jimd80/party-games-26p/images/microbit-battery.png

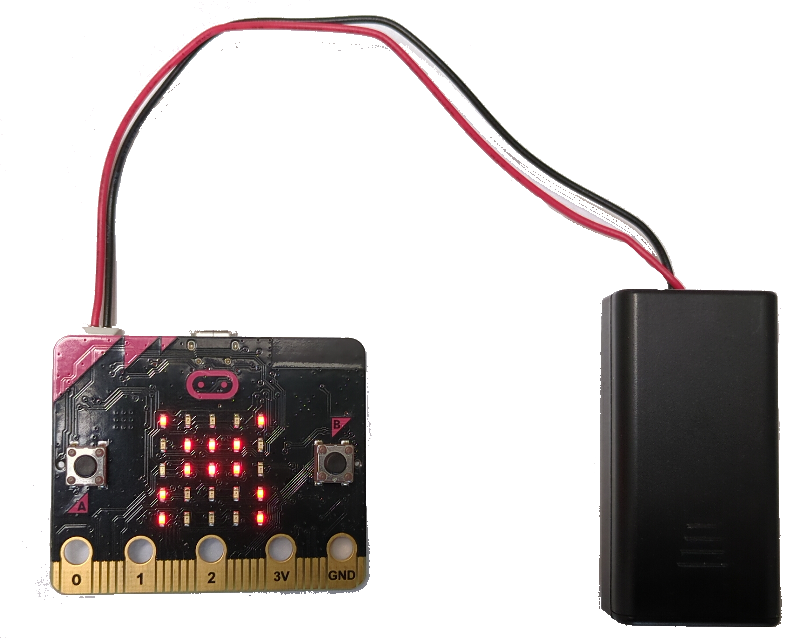
images/microbit-battery.png
