jimd80/party-games-26p/receiver-pcb/CAD-Images/copper_layer_1_top.png

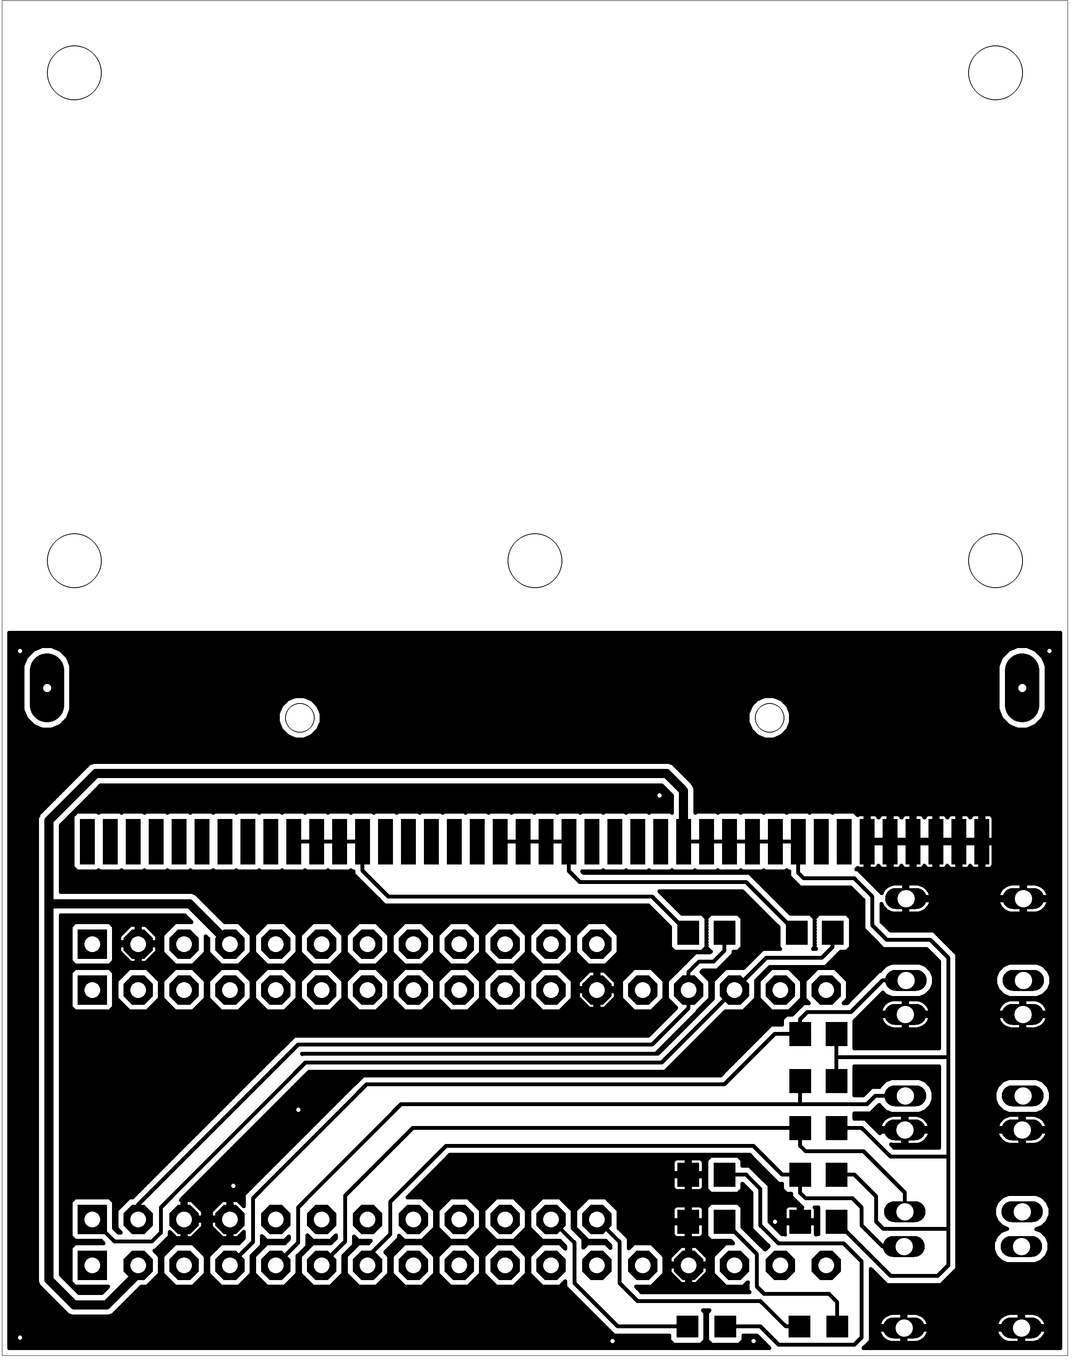
receiver-pcb/CAD-Images/copper_layer_1_top.png
