jimd80/party-games-26p/receiver-pcb/CAD-Images/copper_layer_2_bottom.png

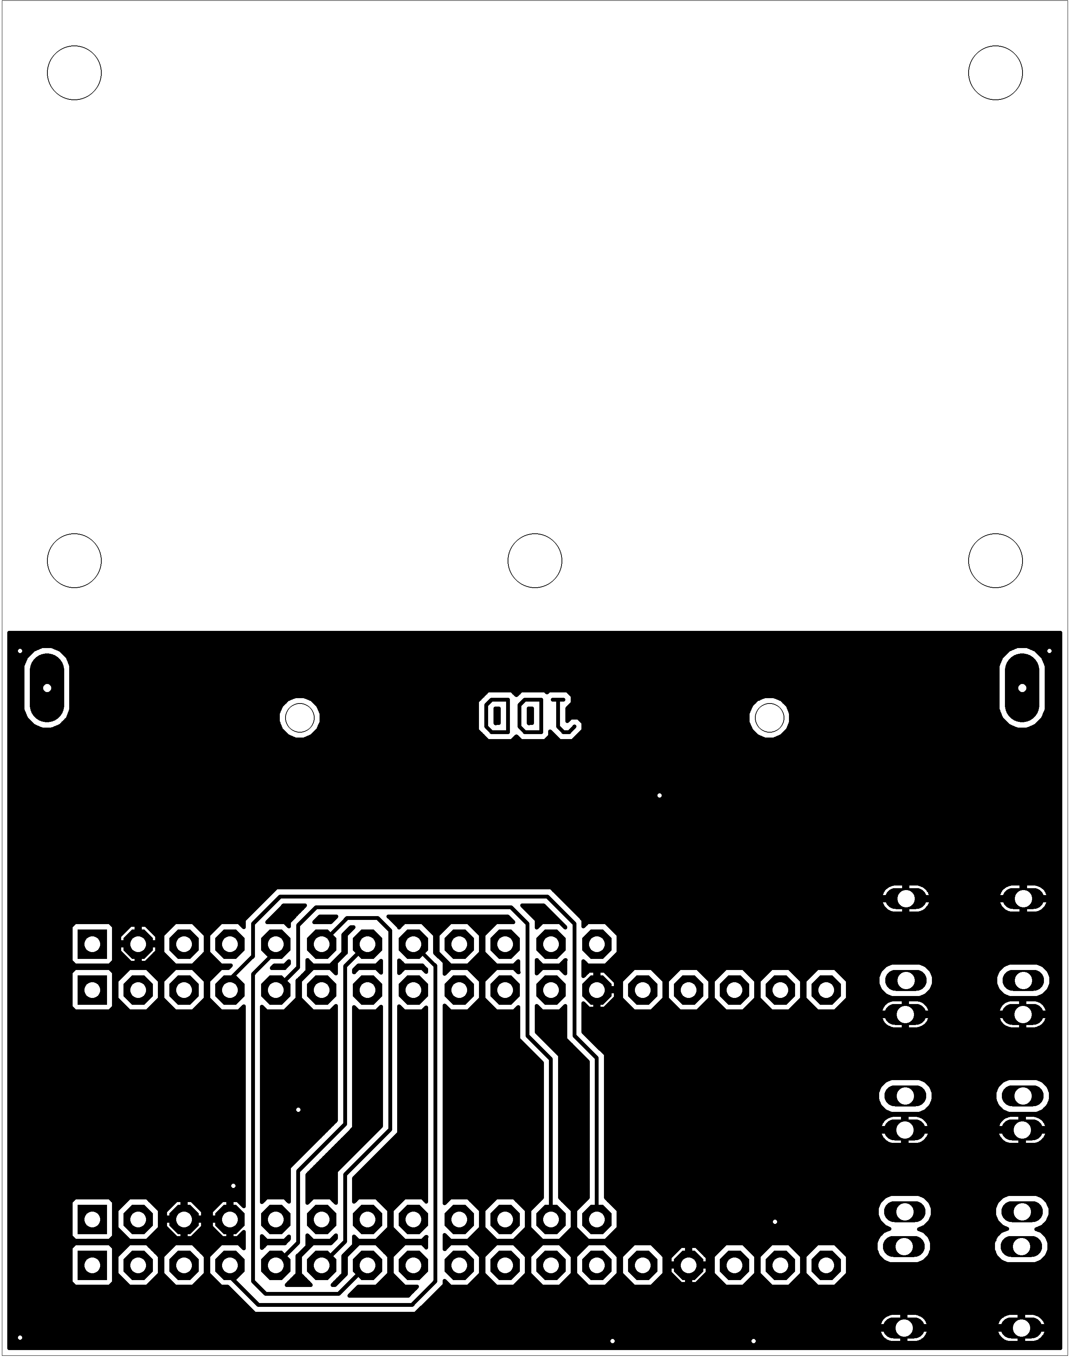
receiver-pcb/CAD-Images/copper_layer_2_bottom.png
