jimd80/party-games-26p/receiver-pcb/CAD-Images/layout.png

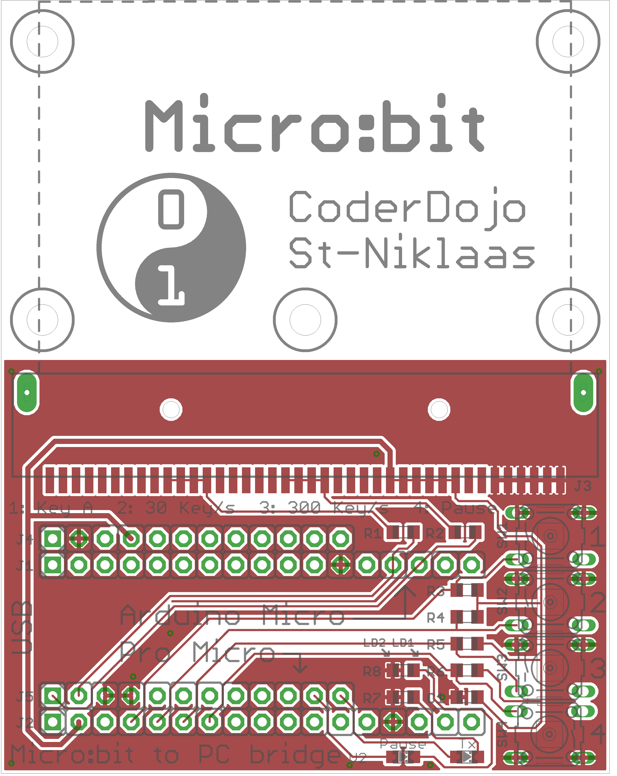
receiver-pcb/CAD-Images/layout.png
