jimd80/party-games-26p/receiver-pcb/CAD-Images/plated_drills.png

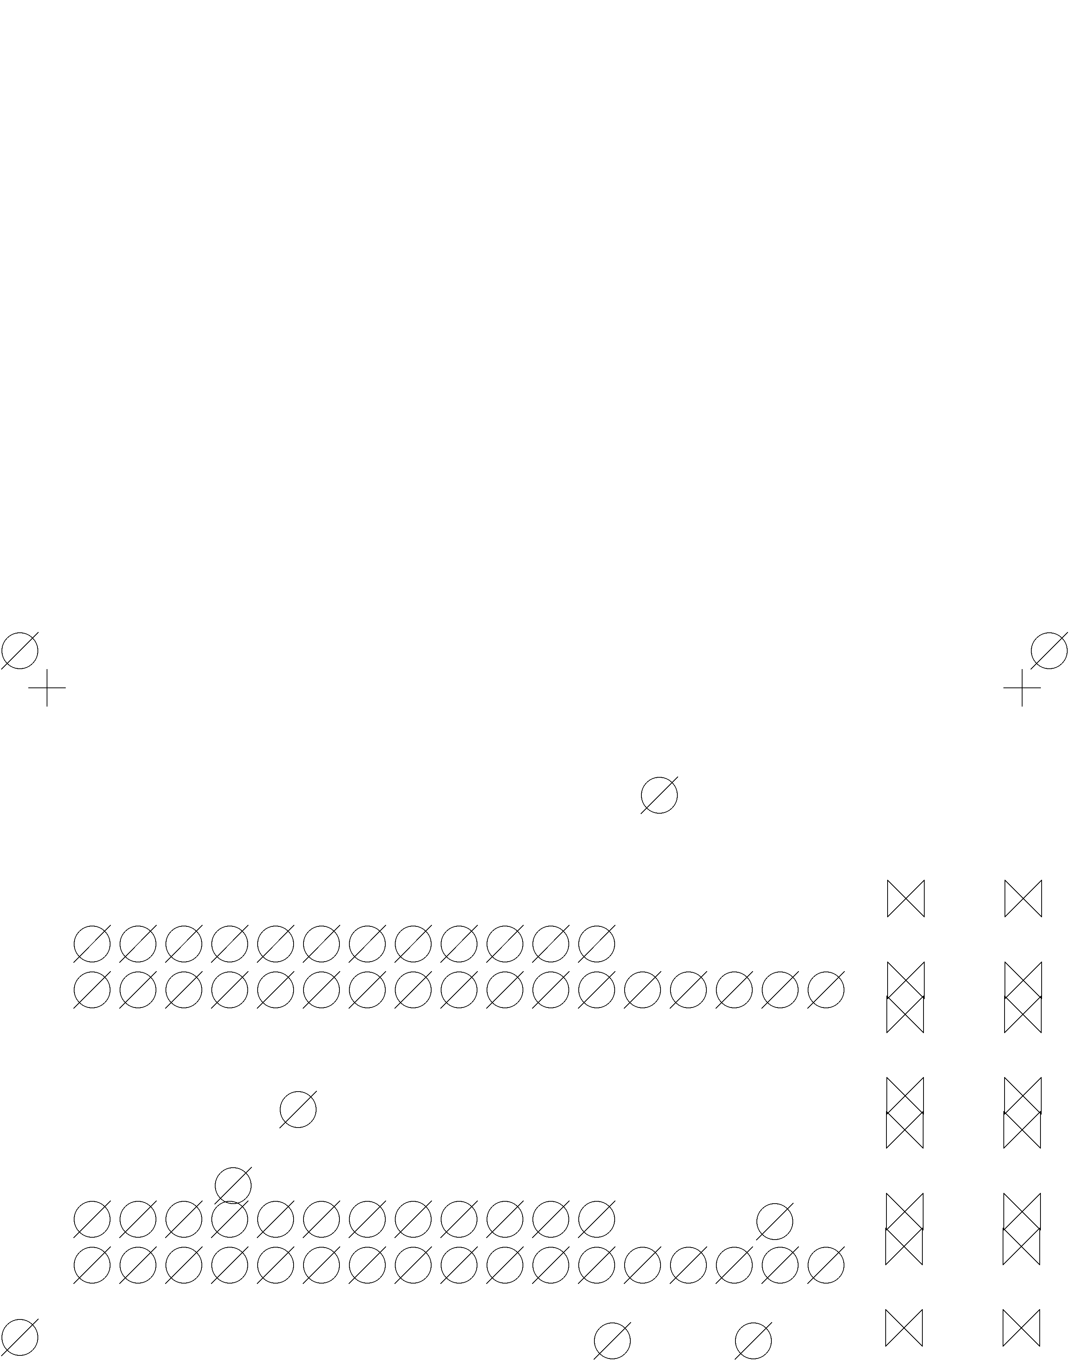
receiver-pcb/CAD-Images/plated_drills.png
