jimd80/party-games-26p/receiver-pcb/CAD-Images/silkscreen_bottom.png

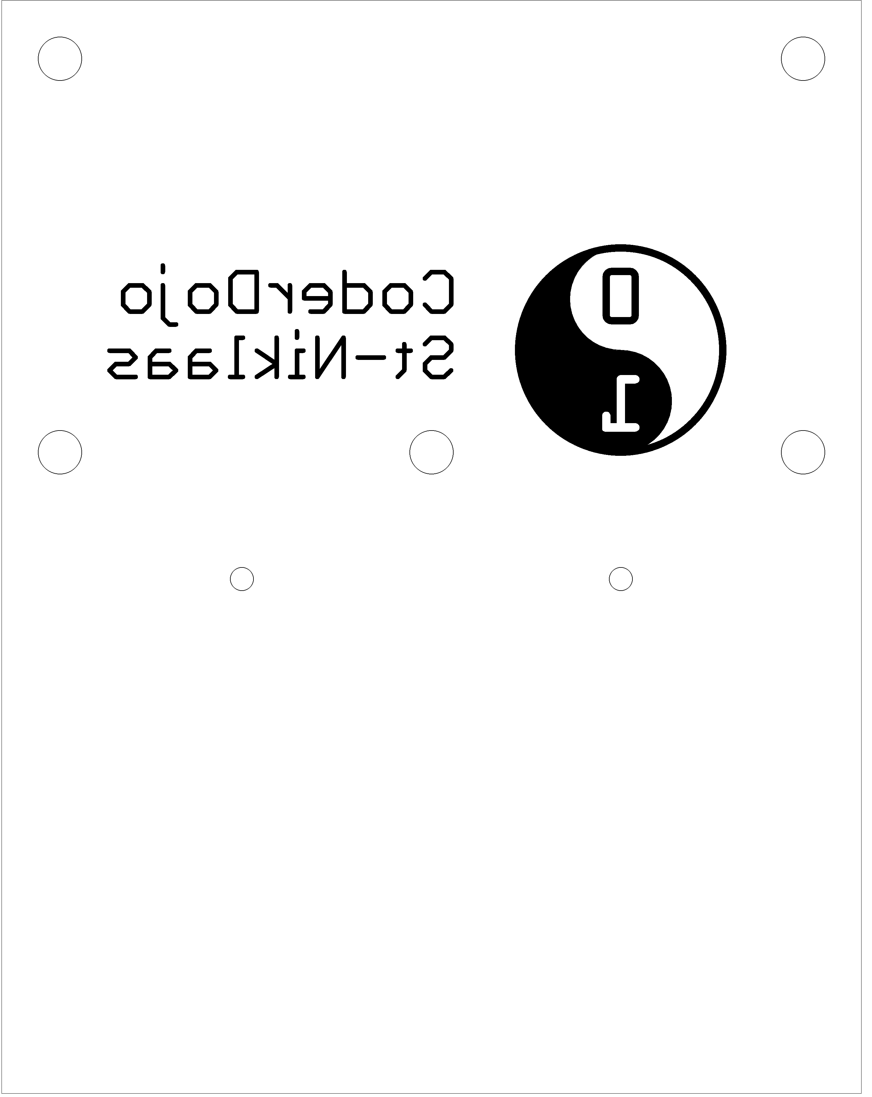
receiver-pcb/CAD-Images/silkscreen_bottom.png
