jimd80/party-games-26p/receiver-pcb/CAD-Images/silkscreen_top.png

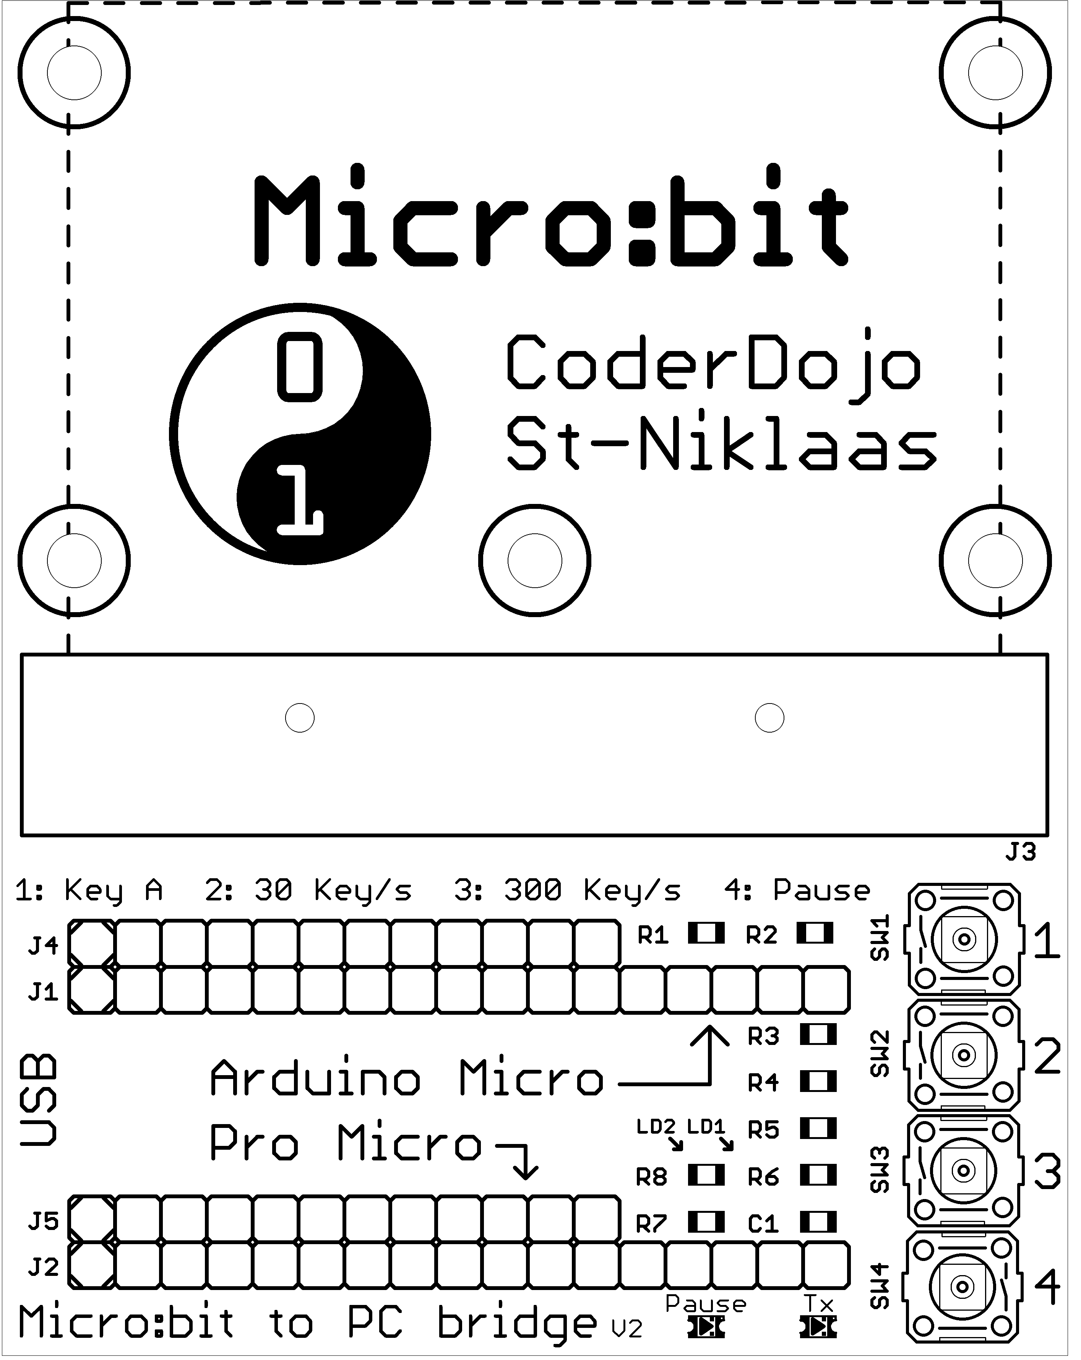
receiver-pcb/CAD-Images/silkscreen_top.png
