jimd80/party-games-26p/receiver-pcb/CAD-Images/unplated_drills.png

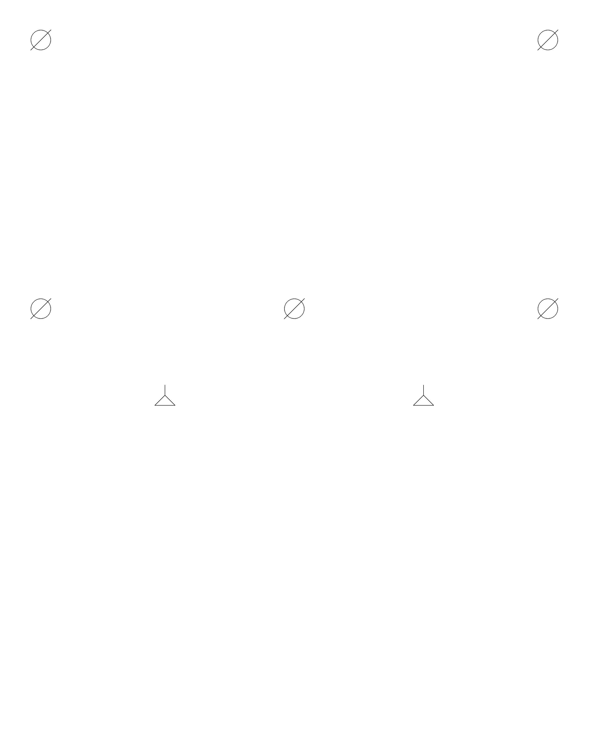
receiver-pcb/CAD-Images/unplated_drills.png
