jimd80/party-games-26p/receiver-pcb/images/Microbit arduino bridge pcb.png

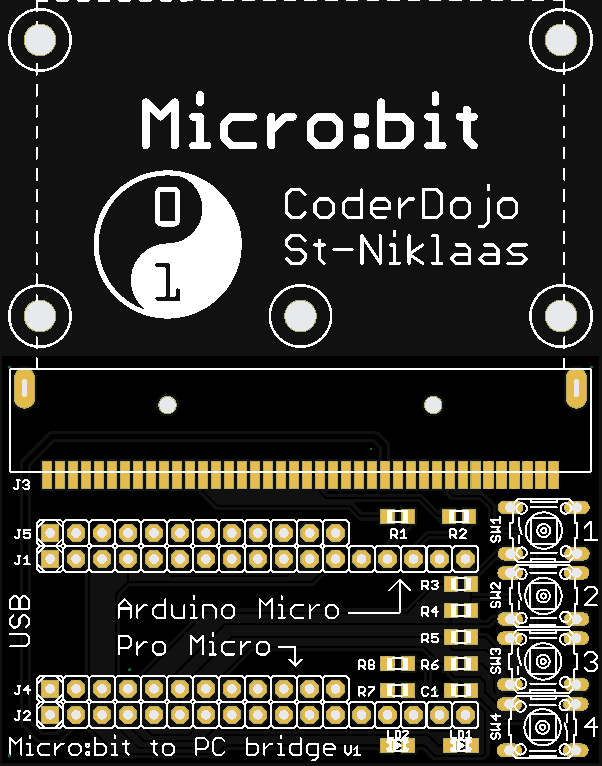
receiver-pcb/images/Microbit arduino bridge pcb.png
