jimd80/party-games-26p/sender-microbit-src/images/Game controllers.jpg

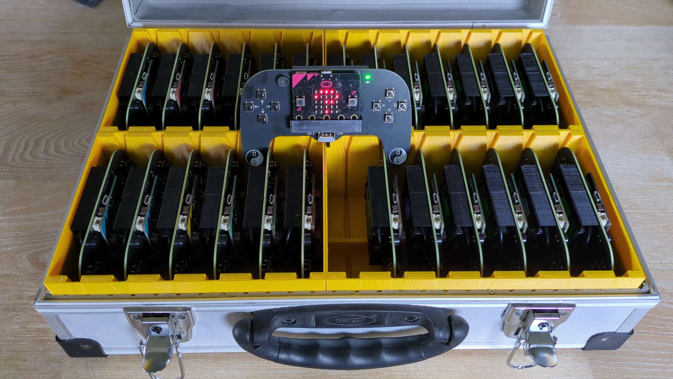
sender-microbit-src/images/Game controllers.jpg
