jimd80/party-games-26p/receiver-arduino-src/src/KeyboardLayout_en_US_numpad.cpp

/*
 * Standard US keyboard layout.
 */

#include "KeyboardLayout.h"

extern const uint8_t KeyboardLayout_en_US_numpad[128] PROGMEM =
{
	0x00,          // NUL
	0x00,          // SOH
	0x00,          // STX
	0x00,          // ETX
	0x00,          // EOT
	0x00,          // ENQ
	0x00,          // ACK
	0x00,          // BEL
	0x2a,          // BS  Backspace
	0x2b,          // TAB Tab
	0x28,          // LF  Enter
	0x00,          // VT
	0x00,          // FF
	0x00,          // CR
	0x00,          // SO
	0x00,          // SI
	0x00,          // DEL
	0x00,          // DC1
	0x00,          // DC2
	0x00,          // DC3
	0x00,          // DC4
	0x00,          // NAK
	0x00,          // SYN
	0x00,          // ETB
	0x00,          // CAN
	0x00,          // EM
	0x28,          // SUB re-used as enter
	0x29,          // ESC
	0x52,          // FS re-used as up arrow
	0x51,          // GS re-used as down arrow
	0x50,          // RS re-used as left arrow
	0x4F,          // US re-used as right arrow

	0x2c,          // ' '
	0x1e|SHIFT,    // !
	0x34|SHIFT,    // "
	0x20|SHIFT,    // #
	0x21|SHIFT,    // $
	0x22|SHIFT,    // %
	0x24|SHIFT,    // &
	0x34,          // '
	0x26|SHIFT,    // (
	0x27|SHIFT,    // )
	0x25|SHIFT,    // *
	0x2e|SHIFT,    // +
	0x36,          // ,
	0x2d,          // -
	0x37,          // .
	0x38,          // /
	0x62,          // 0 (numpad)
	0x59,          // 1 (numpad)
	0x5a,          // 2 (numpad)
	0x5b,          // 3 (numpad)
	0x5c,          // 4 (numpad)
	0x5d,          // 5 (numpad)
	0x5e,          // 6 (numpad)
	0x5f,          // 7 (numpad)
	0x60,          // 8 (numpad)
	0x61,          // 9 (numpad)
	0x33|SHIFT,    // :
	0x33,          // ;
	0x36|SHIFT,    // <
	0x2e,          // =
	0x37|SHIFT,    // >
	0x38|SHIFT,    // ?
	0x1f|SHIFT,    // @
	0x04|SHIFT,    // A
	0x05|SHIFT,    // B
	0x06|SHIFT,    // C
	0x07|SHIFT,    // D
	0x08|SHIFT,    // E
	0x09|SHIFT,    // F
	0x0a|SHIFT,    // G
	0x0b|SHIFT,    // H
	0x0c|SHIFT,    // I
	0x0d|SHIFT,    // J
	0x0e|SHIFT,    // K
	0x0f|SHIFT,    // L
	0x10|SHIFT,    // M
	0x11|SHIFT,    // N
	0x12|SHIFT,    // O
	0x13|SHIFT,    // P
	0x14|SHIFT,    // Q
	0x15|SHIFT,    // R
	0x16|SHIFT,    // S
	0x17|SHIFT,    // T
	0x18|SHIFT,    // U
	0x19|SHIFT,    // V
	0x1a|SHIFT,    // W
	0x1b|SHIFT,    // X
	0x1c|SHIFT,    // Y
	0x1d|SHIFT,    // Z
	0x2f,          // [
	0x31,          // bslash
	0x30,          // ]
	0x23|SHIFT,    // ^
	0x2d|SHIFT,    // _
	0x35,          // `
	0x04,          // a
	0x05,          // b
	0x06,          // c
	0x07,          // d
	0x08,          // e
	0x09,          // f
	0x0a,          // g
	0x0b,          // h
	0x0c,          // i
	0x0d,          // j
	0x0e,          // k
	0x0f,          // l
	0x10,          // m
	0x11,          // n
	0x12,          // o
	0x13,          // p
	0x14,          // q
	0x15,          // r
	0x16,          // s
	0x17,          // t
	0x18,          // u
	0x19,          // v
	0x1a,          // w
	0x1b,          // x
	0x1c,          // y
	0x1d,          // z
	0x2f|SHIFT,    // {
	0x31|SHIFT,    // |
	0x30|SHIFT,    // }
	0x35|SHIFT,    // ~
	0x00           // DEL
};
